mynameisashllee/flowerdle/src/schematic/flowerdle.kicad_sch

## KiCad design src/schematic/flowerdle.kicad_sch (2025-07-14)

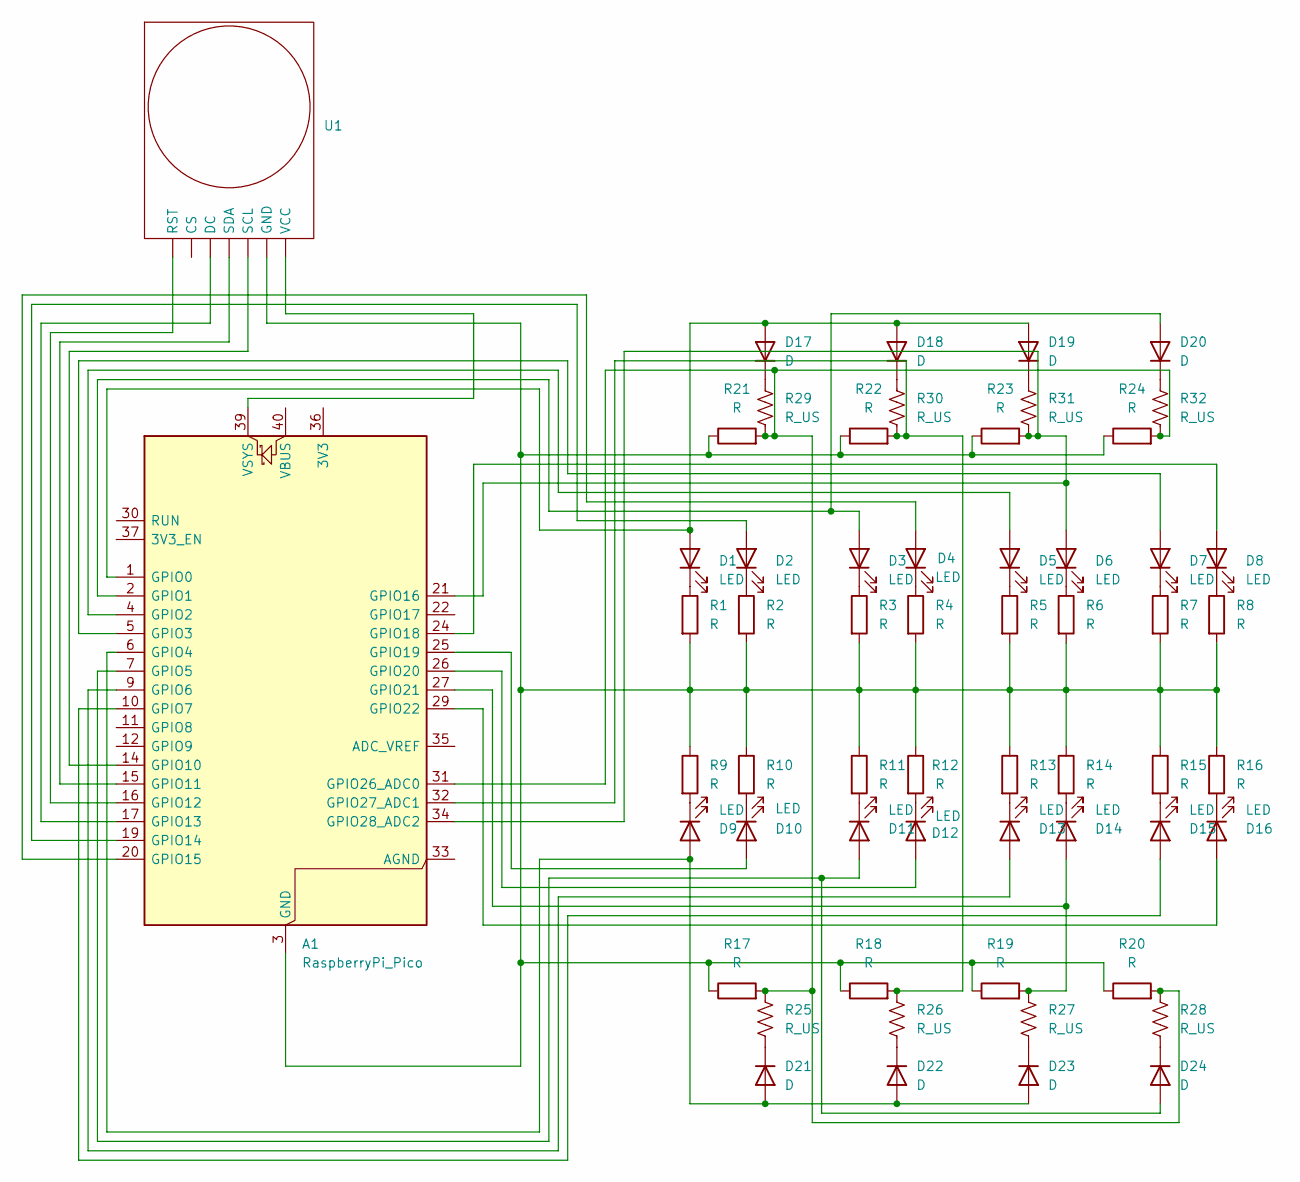
[picture p34: schematic flowerdle.kicad_sch]

Parts:
A1: RaspberryPi_Pico; RaspberryPi_Pico_Common_Unspecified
D1, D2, D3, D4, D5, D6, D7, D8, D9, D10, D11, D12, D13, D14, D15, D16: LED
D17, D18, D19, D20, D21, D22, D23, D24: D
R1, R2, R3, R4, R5, R6, R7, R8, R9, R10, R11, R12, R13, R14, R15, R16, R17, R18, R19, R20, R21, R22, R23, R24: R
R25, R26, R27, R28, R29, R30, R31, R32: R_US
U1: (no value)

Connections:
unnamed: A1.1 (GPIO0), D1.2 (A), D17.2 (A), D18.2 (A), D19.2 (A)
unnamed: A1.2 (GPIO1), D3.2 (A), D20.2 (A)
unnamed: A1.4 (GPIO2), D5.2 (A)
unnamed: A1.5 (GPIO3), D7.2 (A)
unnamed: A1.6 (GPIO4), D9.2 (A), D21.2 (A), D22.2 (A), D23.2 (A)
unnamed: A1.7 (GPIO5), D11.2 (A), D24.2 (A)
unnamed: A1.9 (GPIO6), D13.2 (A)
unnamed: A1.10 (GPIO7), D15.2 (A)
unnamed: A1.3 (GND), A1.8 (GND), A1.13 (GND), A1.18 (GND), A1.23 (GND), A1.28 (GND), A1.38 (GND), R1.2, R2.2, R3.2, R4.2, R5.2, R6.2, R7.2, R8.2, R9.1, R10.1, R11.1, R12.1, R13.1, R14.1, R15.1, R16.1, R17.1, R18.1, R19.1, R20.1, R21.1, R22.1, R23.1, R24.1, U1.
unnamed: A1.14 (GPIO10), U1.
unnamed: A1.15 (GPIO11), U1.
unnamed: A1.16 (GPIO12), U1.
unnamed: A1.17 (GPIO13), U1.
unnamed: A1.19 (GPIO14), D2.2 (A)
unnamed: A1.20 (GPIO15), D4.2 (A)
unnamed: A1.21 (GPIO16), A1.34 (GPIO28_ADC2), D6.2 (A), R23.2, R31.2
unnamed: A1.24 (GPIO18), D8.2 (A)
unnamed: A1.25 (GPIO19), D10.2 (A)
unnamed: A1.26 (GPIO20), D12.2 (A)
unnamed: A1.27 (GPIO21), D14.2 (A), R19.2, R27.1
unnamed: A1.29 (GPIO22), D16.2 (A)
unnamed: A1.31 (GPIO26_ADC0), R17.2, R20.2, R21.2, R24.2, R25.1, R28.1, R29.2, R32.2
unnamed: A1.32 (GPIO27_ADC1), R18.2, R22.2, R26.1, R30.2
unnamed: A1.39 (VSYS), U1.
unnamed: D1.1 (K), R1.1
unnamed: D2.1 (K), R2.1
unnamed: D3.1 (K), R3.1
unnamed: D4.1 (K), R4.1
unnamed: D5.1 (K), R5.1
unnamed: D6.1 (K), R6.1
unnamed: D7.1 (K), R7.1
unnamed: D8.1 (K), R8.1
unnamed: D9.1 (K), R9.2
unnamed: D10.1 (K), R10.2
unnamed: D11.1 (K), R11.2
unnamed: D12.1 (K), R12.2
unnamed: D13.1 (K), R13.2
unnamed: D14.1 (K), R14.2
unnamed: D15.1 (K), R15.2
unnamed: D16.1 (K), R16.2
unnamed: D17.1 (K), R29.1
unnamed: D18.1 (K), R30.1
unnamed: D19.1 (K), R31.1
unnamed: D20.1 (K), R32.1
unnamed: D21.1 (K), R25.2
unnamed: D22.1 (K), R26.2
unnamed: D23.1 (K), R27.2
unnamed: D24.1 (K), R28.2
